scipioni/clavis/firmware/zmk-timeless/miryoku/miryoku_behaviors.h

// Copyright 2022 Manna Harbour
// https://github.com/manna-harbour/miryoku

#pragma once

#define U_MT(MOD, TAP) &u_mt MOD TAP
#define U_LT(LAYER, TAP) &u_lt LAYER TAP


// with hold-trigger-key-positions
#define U_MTL(MOD, TAP) &hrm_l MOD TAP
#define U_MTR(MOD, TAP) &hrm_r MOD TAP

#define U_LTL(LAYER, TAP) &lm_l LAYER TAP
#define U_LTR(LAYER, TAP) &lm_r LAYER TAP
